ThunderFly-aerospace/6axis-platform/CAD/src/printplate/printplate_888_4001.scad

include <../../../parameters.scad>
include <../calculations.scad>


//@set_slicing_config(../../slicing/strong.ini)

//dil pro pripevneni priruby magnetu
use <../888_4001.scad>

888_4001(false);
