ThunderFly-aerospace/6axis-platform/CAD/png/printplate_888_4006.png

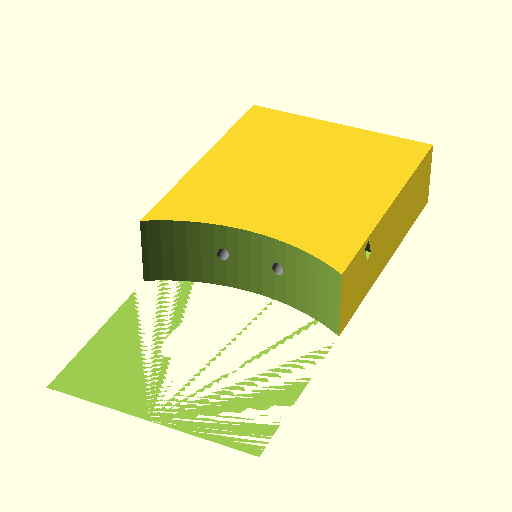
CAD/png/printplate_888_4006.png
