ThunderFly-aerospace/6axis-platform/sw/position_measurement/data/test_board.png

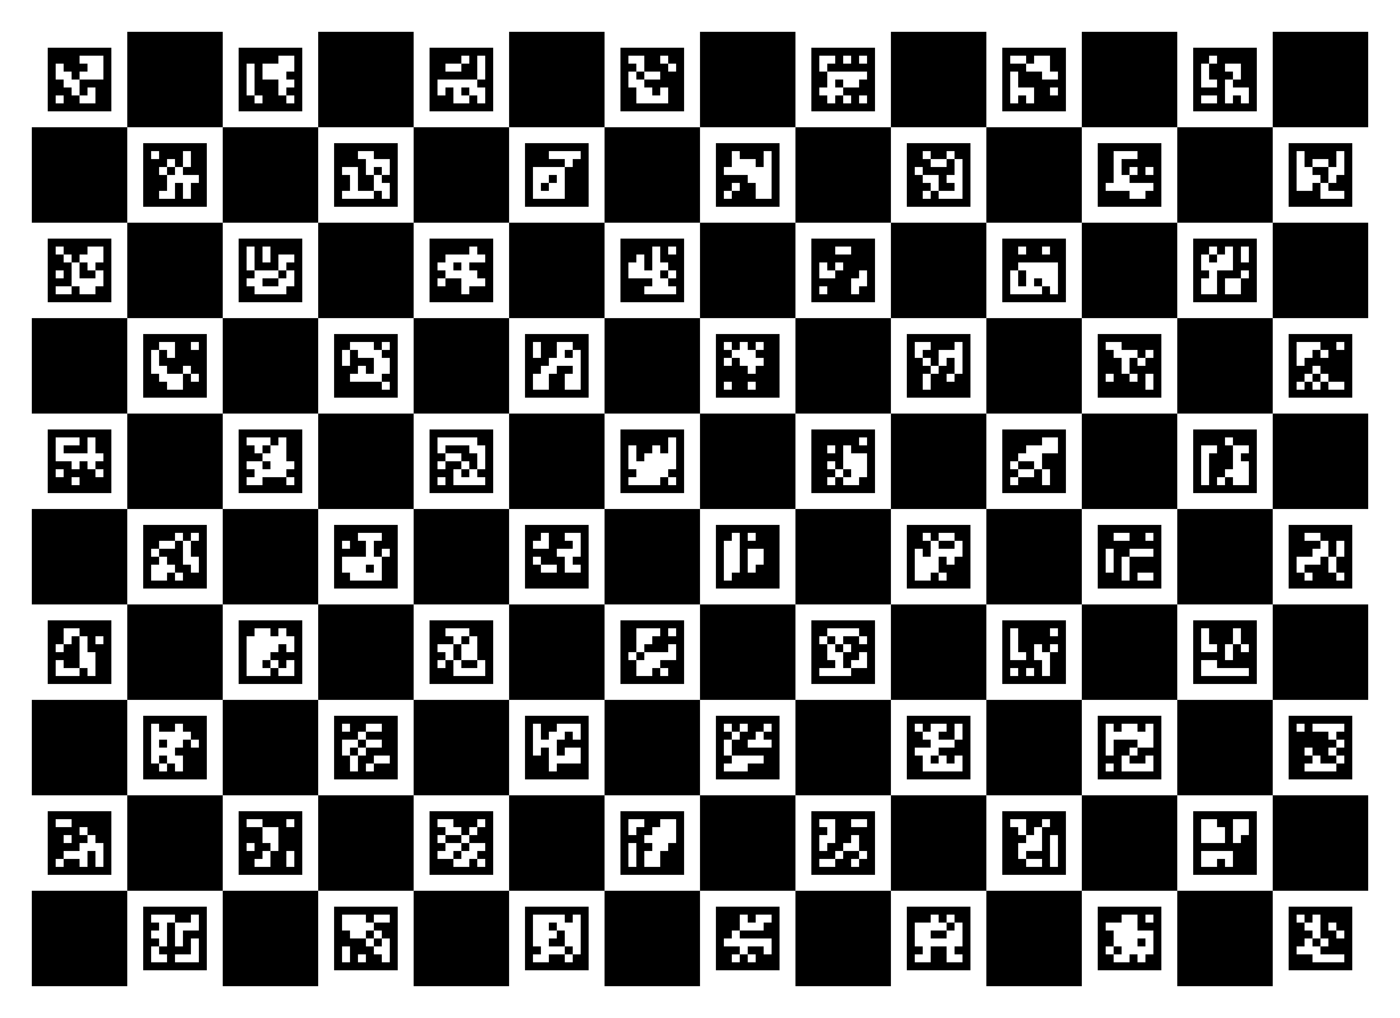
sw/position_measurement/data/test_board.png
